hierle/letterbox-sensor/PCB/lora2.jpg

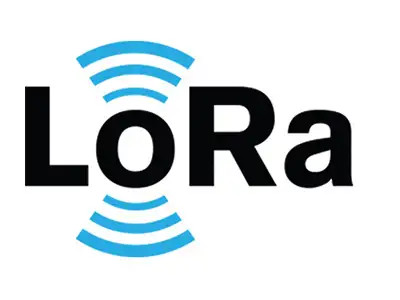
PCB/lora2.jpg
